Duckle29/WiFIR/firmware/src/main.h

#include <Arduino.h>

// WiFiManager imports
#include <ESP8266WiFi.h>
#include <DNSServer.h>
#include <ESP8266WebServer.h>
#include <WiFiManager.h>


// Prototypes
char * uintToStr( const uint64_t, char *);
void schlep(uint64_t);
